Kozma04/Tiny-FM-Radio/media/IMG_20210413_210414.jpg

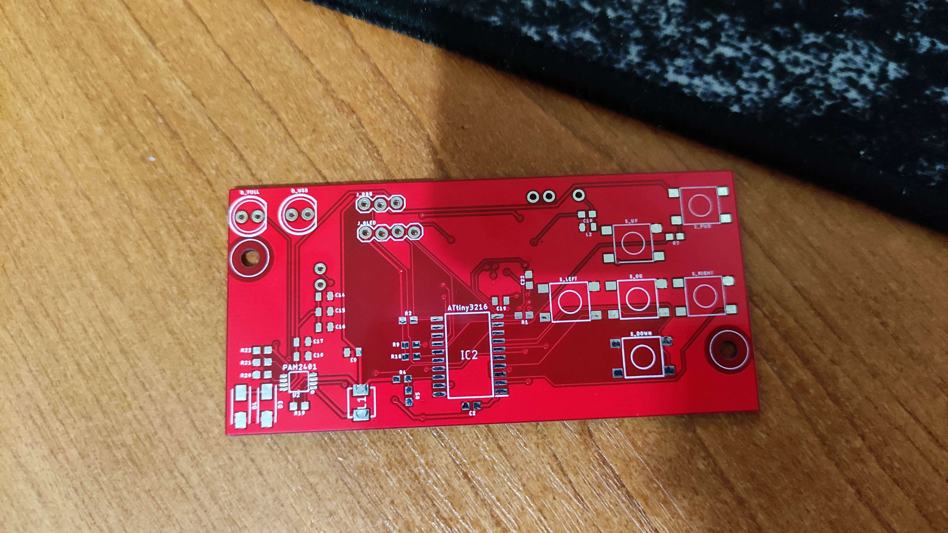
media/IMG_20210413_210414.jpg
