Kozma04/Tiny-FM-Radio/media/IMG_20210420_195142.jpg

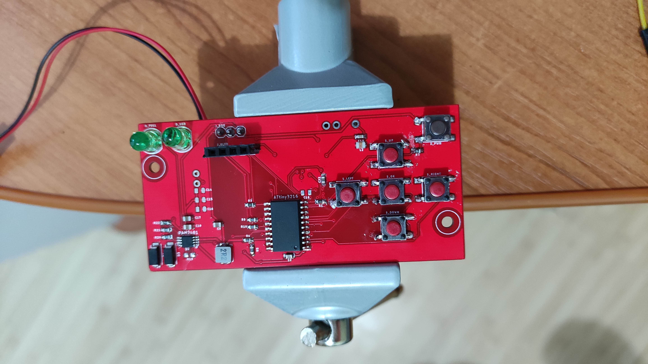
media/IMG_20210420_195142.jpg
