Kozma04/Tiny-FM-Radio/media/IMG_20210421_002226.jpg

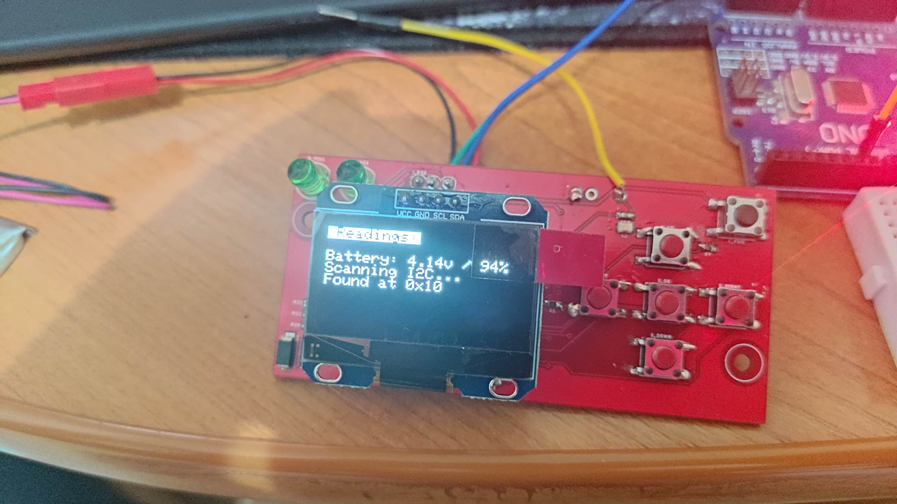
media/IMG_20210421_002226.jpg
