Kozma04/Tiny-FM-Radio/media/IMG_20210424_092515.jpg

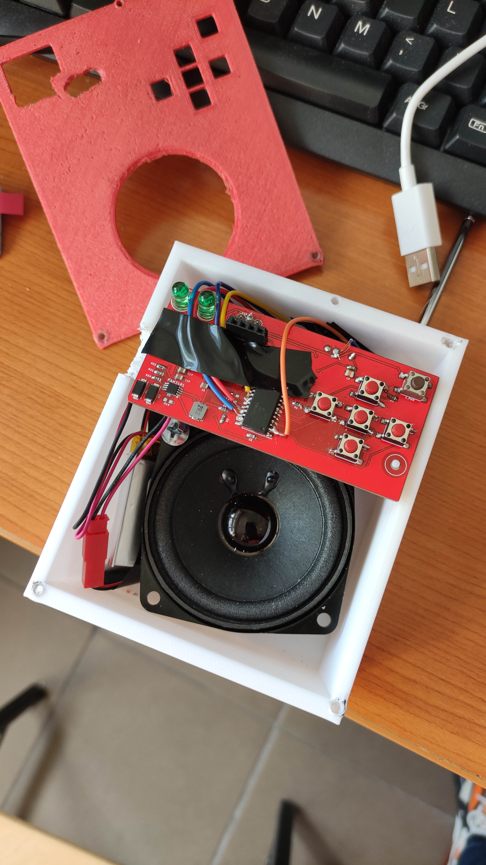
media/IMG_20210424_092515.jpg
